Rom3oDelta7/MailNotifier/MailboxNotifier/locals.h

/*
 local definitions, not part of github public repo
 */
 
char auth[] = "<insert Blynk authorization code here>";
char ssid[] = "<your SSID>";
char pass[] = "<your WiFi password>";

#define SMS_EMAIL			"<your text message email address>"		// email address for text messages, e.g. 408.123.4567@vtext.com
